firestaradmin/mPower/mPower/image-20230119194510718.png

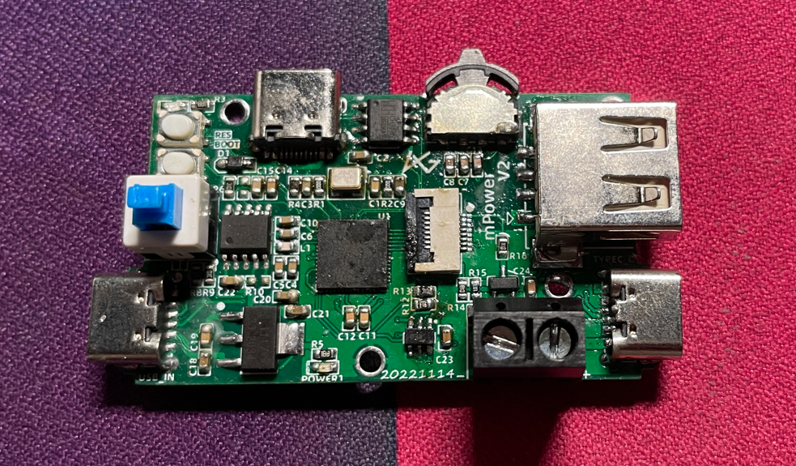
mPower/image-20230119194510718.png
